brian200508/Marlin/docs/brsc/FTI-1.0.x/pictures/IMG_20200317_183908.jpg

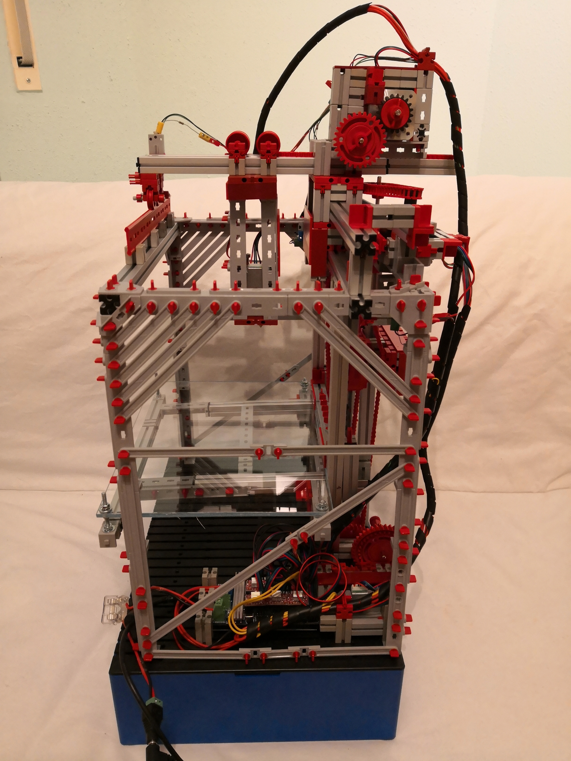
docs/brsc/FTI-1.0.x/pictures/IMG_20200317_183908.jpg
