brian200508/Marlin/docs/brsc/FTI-1.1.x/pictures/IMG_20200419_235620.jpg

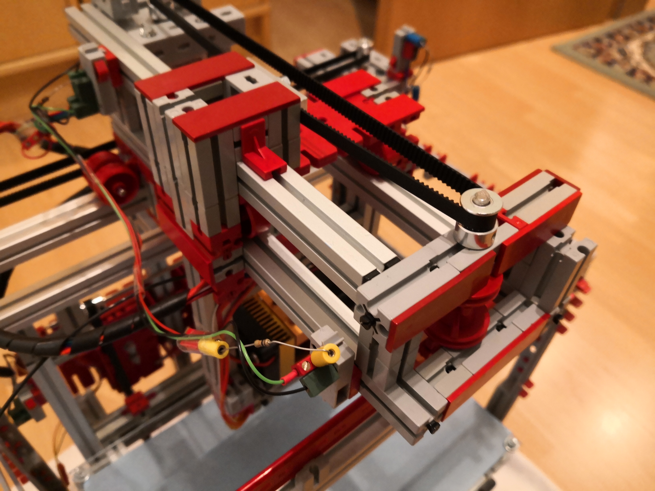
docs/brsc/FTI-1.1.x/pictures/IMG_20200419_235620.jpg
