brian200508/Marlin/docs/brsc/FTI-1.2.x/pictures/IMG_20200604_142323.jpg

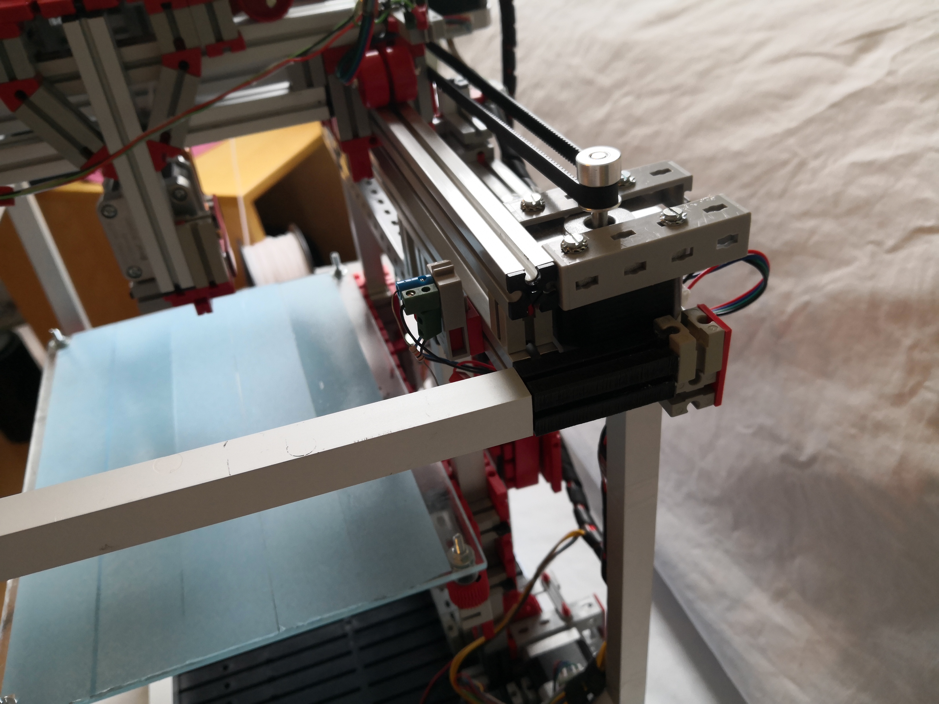
docs/brsc/FTI-1.2.x/pictures/IMG_20200604_142323.jpg
