brian200508/Marlin/docs/brsc/FTI-1.2.x/custom-parts/not-used/aluminum-square-tube-15x15-to-Fischertechnik-adapter-x-y-15-X-Z.png

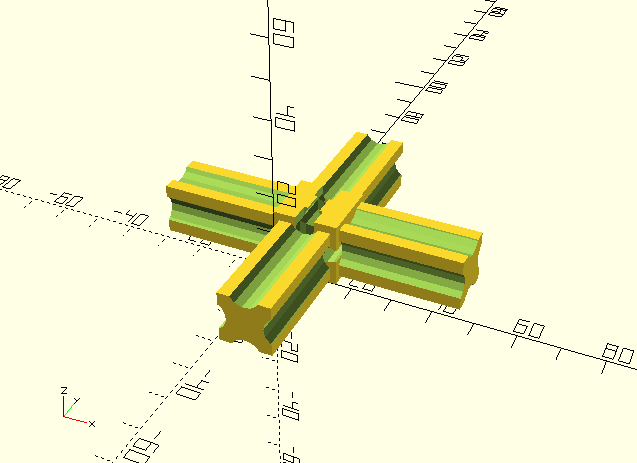
docs/brsc/FTI-1.2.x/custom-parts/not-used/aluminum-square-tube-15x15-to-Fischertechnik-adapter-x-y-15-X-Z.png
