brian200508/Marlin/docs/brsc/FTI-1.2.x/custom-parts/not-used/aluminum-square-tube-15x15-to-Fischertechnik-adapter-y-z-15-T.png

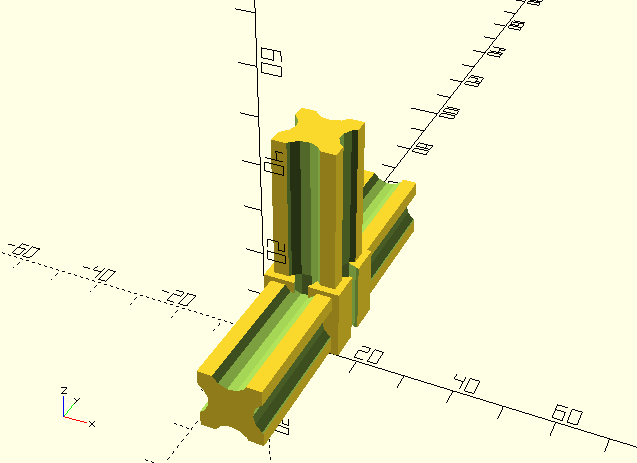
docs/brsc/FTI-1.2.x/custom-parts/not-used/aluminum-square-tube-15x15-to-Fischertechnik-adapter-y-z-15-T.png
