brian200508/Marlin/docs/brsc/FTI-1.2.x/custom-parts/not-used/axis-5mm-to-4mm-Fischertechnik-adapter.png

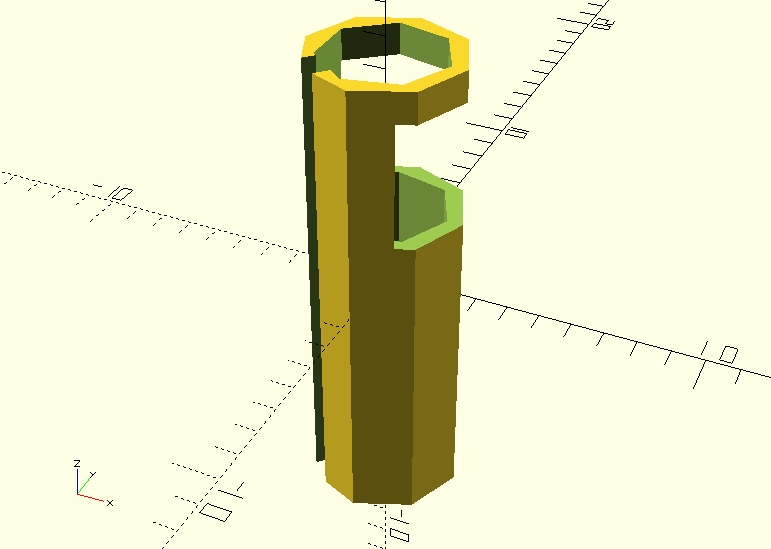
docs/brsc/FTI-1.2.x/custom-parts/not-used/axis-5mm-to-4mm-Fischertechnik-adapter.png
