brian200508/Marlin/docs/brsc/FTI-1.2.x/custom-parts/thingiverse/Belt_Tensioner_-_Reinforced/images/98af658794dd09332cecc4e60c305fb2_preview_featured.jpg

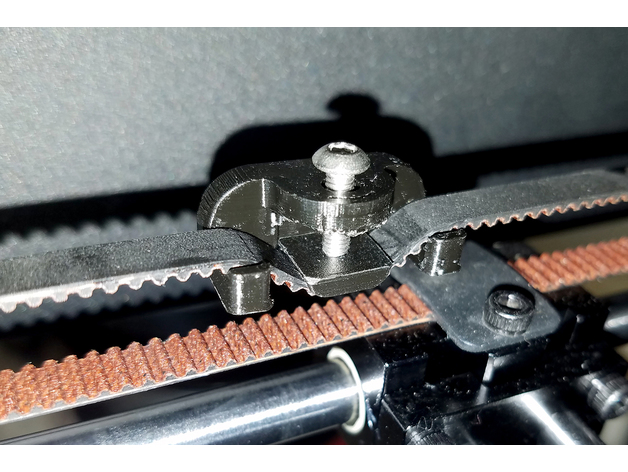
docs/brsc/FTI-1.2.x/custom-parts/thingiverse/Belt_Tensioner_-_Reinforced/images/98af658794dd09332cecc4e60c305fb2_preview_featured.jpg
