brian200508/Marlin/docs/brsc/FTI-1.2.x/custom-parts/thingiverse/Belt_Tensioner_-_Reinforced/images/16809a94bf5a926e6fb144e2bca0509e_preview_featured.jpg

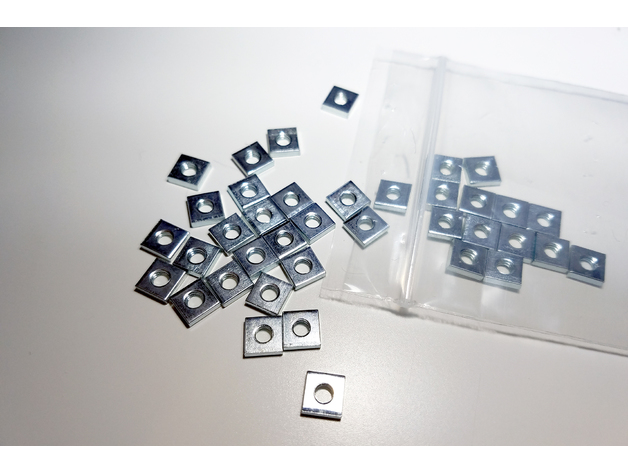
docs/brsc/FTI-1.2.x/custom-parts/thingiverse/Belt_Tensioner_-_Reinforced/images/16809a94bf5a926e6fb144e2bca0509e_preview_featured.jpg
