brian200508/Marlin/docs/brsc/FTI-1.2.x/custom-parts/thingiverse/Belt_Tensioner_-_Reinforced/images/d638693b8d8fdc0d19c9fbcd61633dfa_preview_featured.jpg

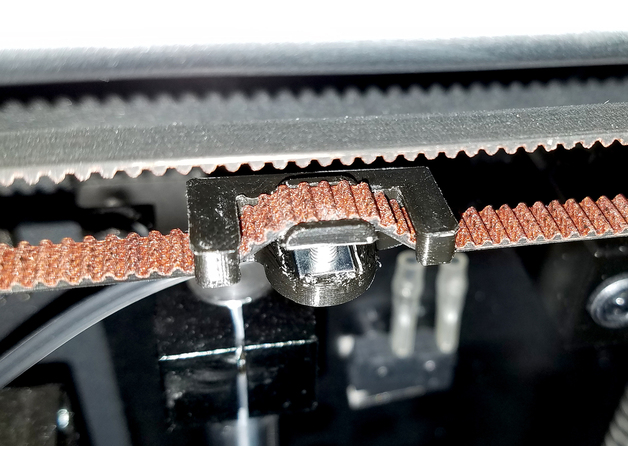
docs/brsc/FTI-1.2.x/custom-parts/thingiverse/Belt_Tensioner_-_Reinforced/images/d638693b8d8fdc0d19c9fbcd61633dfa_preview_featured.jpg
