brian200508/Marlin/docs/brsc/FTI-1.2.x/custom-parts/thingiverse/fischertechnik_double_flat_connector/images/2f4ae6def363fac59a60dda25eb9f56f_preview_featured.JPG

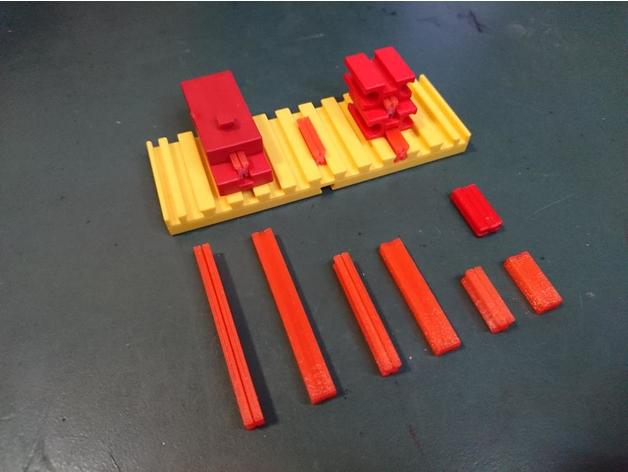
docs/brsc/FTI-1.2.x/custom-parts/thingiverse/fischertechnik_double_flat_connector/images/2f4ae6def363fac59a60dda25eb9f56f_preview_featured.JPG
