brian200508/Marlin/docs/brsc/FTI-1.2.x/custom-parts/thingiverse/fischertechnik_double_flat_connector/images/765520e2c20b9f5ceb8f800691d65215_preview_featured.jpg

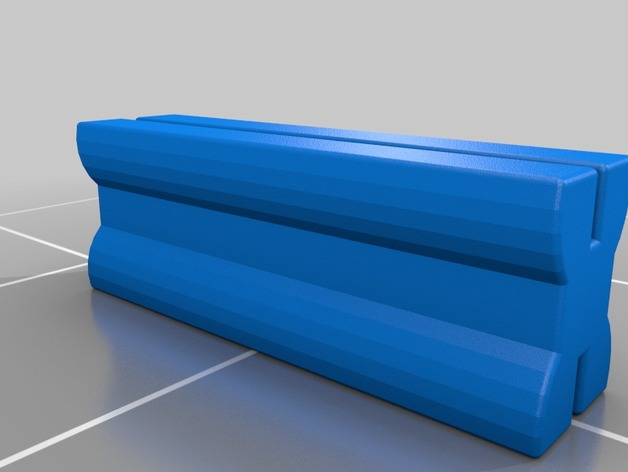
docs/brsc/FTI-1.2.x/custom-parts/thingiverse/fischertechnik_double_flat_connector/images/765520e2c20b9f5ceb8f800691d65215_preview_featured.jpg
