brian200508/Marlin/docs/brsc/FTI-1.2.x/custom-parts/thingiverse/fischertechnik_double_flat_connector/images/ac41eda1f4030cfab85e3fee53aedb6f_preview_featured.jpg

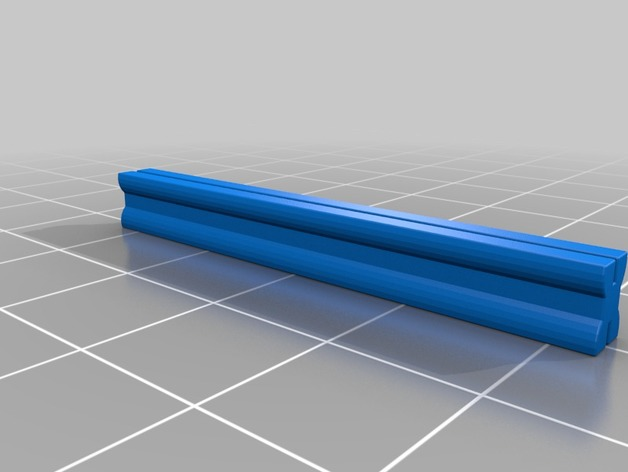
docs/brsc/FTI-1.2.x/custom-parts/thingiverse/fischertechnik_double_flat_connector/images/ac41eda1f4030cfab85e3fee53aedb6f_preview_featured.jpg
