brian200508/Marlin/docs/brsc/FTI-1.2.x/custom-parts/thingiverse/fischertechnik_double_flat_connector/images/b0776671d210ffe9cd5a600b5e34c5cb_preview_featured.jpg

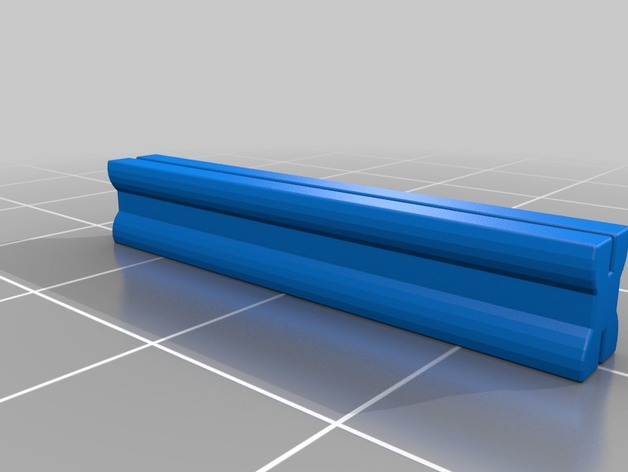
docs/brsc/FTI-1.2.x/custom-parts/thingiverse/fischertechnik_double_flat_connector/images/b0776671d210ffe9cd5a600b5e34c5cb_preview_featured.jpg
