brian200508/Marlin/docs/brsc/FTI-1.2.x/custom-parts/thingiverse/fischertechnik_double_flat_connector/images/d80029e1d572c3cbf382a6284b248c5f_preview_featured.jpg

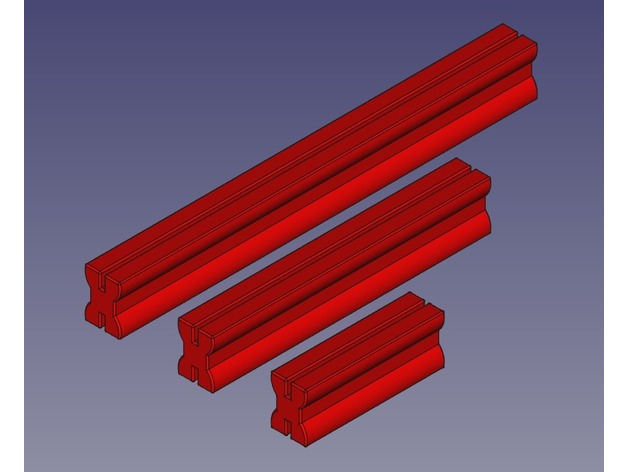
docs/brsc/FTI-1.2.x/custom-parts/thingiverse/fischertechnik_double_flat_connector/images/d80029e1d572c3cbf382a6284b248c5f_preview_featured.jpg
