brian200508/Marlin/docs/brsc/FTI-1.2.x/custom-parts/thingiverse/Fischertechnik_Double_GroovePin_SmartLab/images/058e439d927dcbf255e2c4b969152c6c_preview_featured.jpg

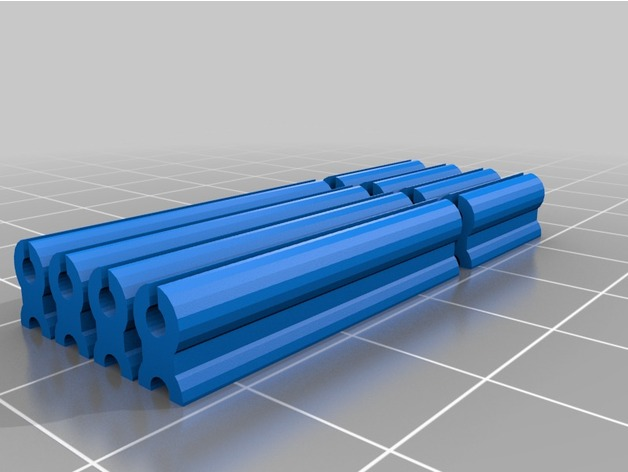
docs/brsc/FTI-1.2.x/custom-parts/thingiverse/Fischertechnik_Double_GroovePin_SmartLab/images/058e439d927dcbf255e2c4b969152c6c_preview_featured.jpg
