brian200508/Marlin/docs/brsc/FTI-1.2.x/custom-parts/thingiverse/Fischertechnik_Double_GroovePin_SmartLab/images/e607530fb95e5e1ce42673f375322e12_preview_featured.JPG

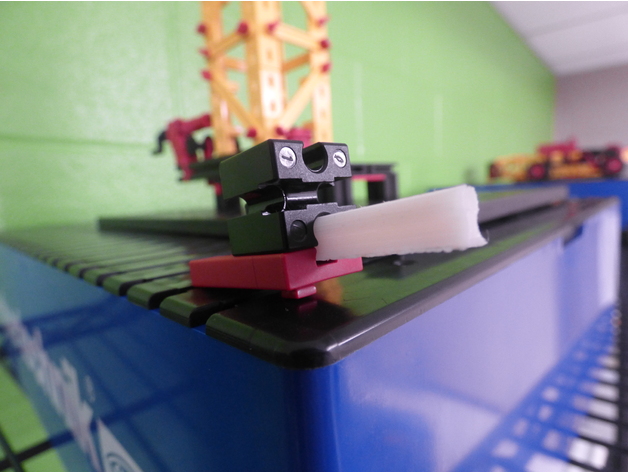
docs/brsc/FTI-1.2.x/custom-parts/thingiverse/Fischertechnik_Double_GroovePin_SmartLab/images/e607530fb95e5e1ce42673f375322e12_preview_featured.JPG
