brian200508/Marlin/docs/brsc/FTI-1.2.x/custom-parts/aluminum-square-tube-15x15-to-Fischertechnik-adapter-15.stl

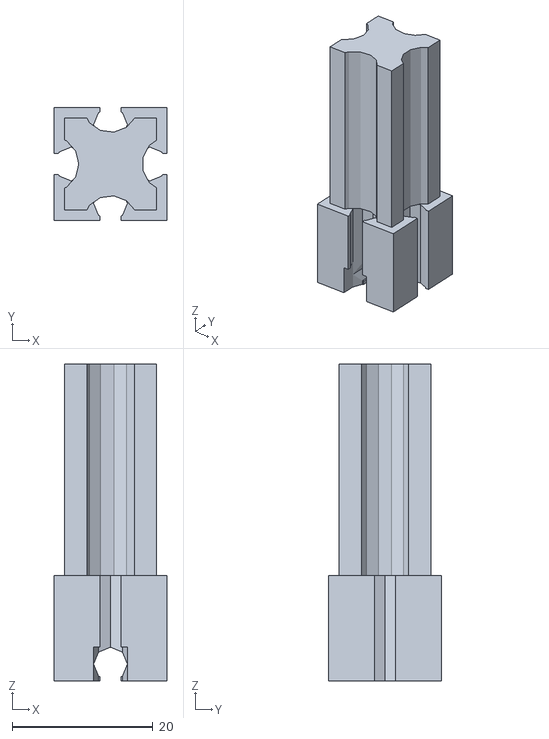
[picture p79: CAD file, 2020-05-04]
docs/brsc/FTI-1.2.x/custom-parts/aluminum-square-tube-15x15-to-Fischertechnik-adapter-15.stl
16.0 x 16.0 x 45.0
