brian200508/Marlin/docs/brsc/FTI-1.2.x/custom-parts/not-used/aluminum-square-tube-15x15-to-Fischertechnik-adapter-30.stl

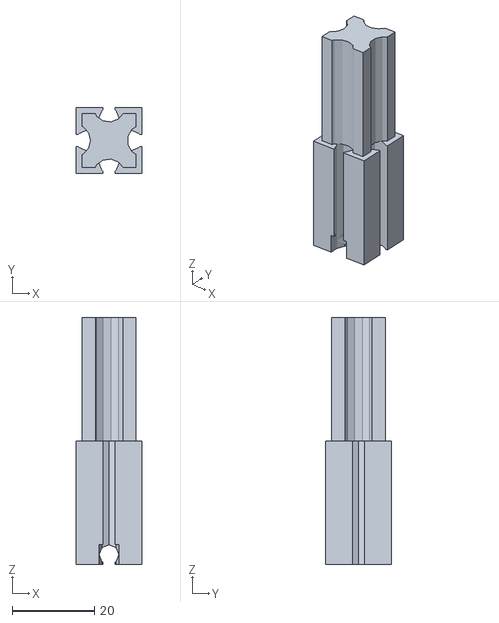
[picture p80: CAD file, 2020-05-04]
docs/brsc/FTI-1.2.x/custom-parts/not-used/aluminum-square-tube-15x15-to-Fischertechnik-adapter-30.stl
16.0 x 16.0 x 60.0
