brian200508/Marlin/docs/brsc/FTI-1.2.x/custom-parts/aluminum-square-tube-15x15-to-Fischertechnik-adapter-x-y-z-15-R.stl

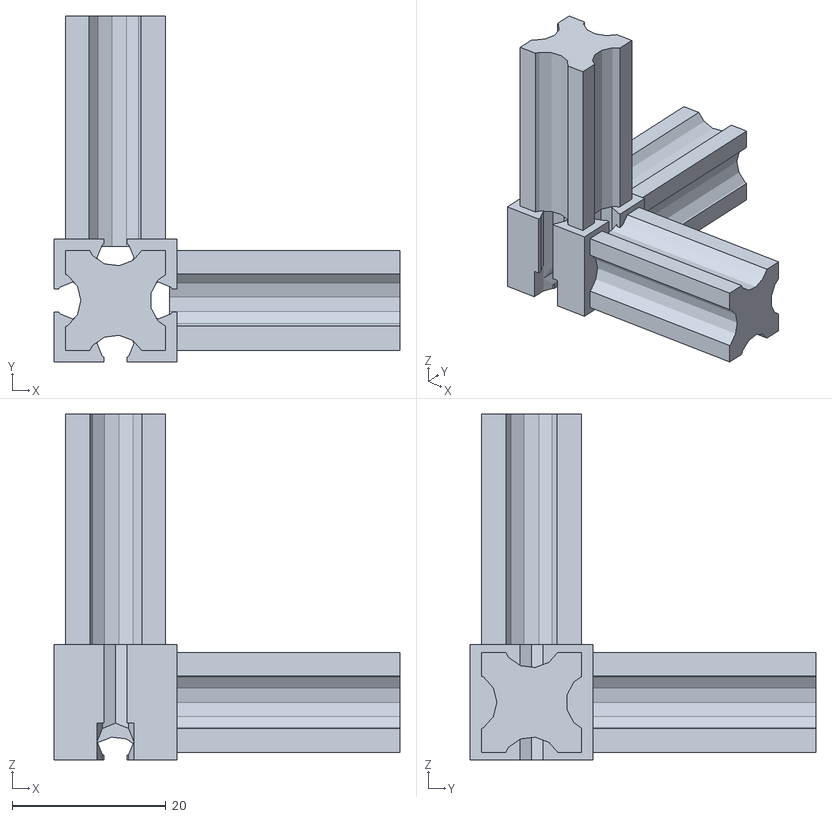
[picture p81: CAD file, 2020-05-04]
docs/brsc/FTI-1.2.x/custom-parts/aluminum-square-tube-15x15-to-Fischertechnik-adapter-x-y-z-15-R.stl
45.0 x 45.0 x 45.0
