brian200508/Marlin/docs/brsc/FTI-1.2.x/custom-parts/not-used/Fischertechnik-compatible-building-block-with-hole-90.stl

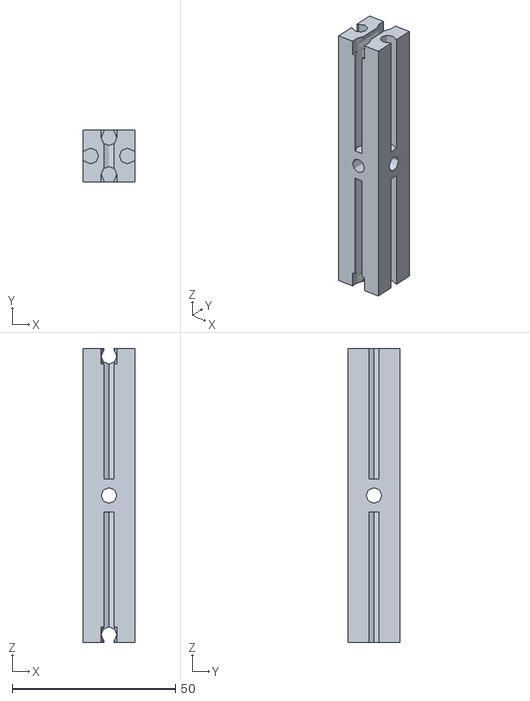
[picture p82: CAD file, 2020-04-23]
docs/brsc/FTI-1.2.x/custom-parts/not-used/Fischertechnik-compatible-building-block-with-hole-90.stl
16.0 x 16.0 x 90.0
