brian200508/Marlin/docs/brsc/FTI-1.2.x/pictures/intermediate-step-1/IMG_20200503_225055.jpg

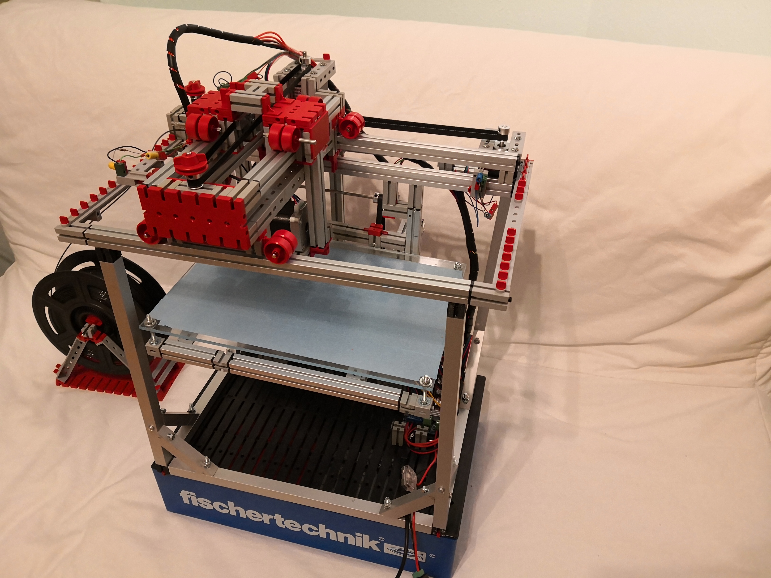
docs/brsc/FTI-1.2.x/pictures/intermediate-step-1/IMG_20200503_225055.jpg
