brian200508/Marlin/docs/brsc/FTI-1.2.x/pictures/intermediate-step-1/IMG_20200503_230231.jpg

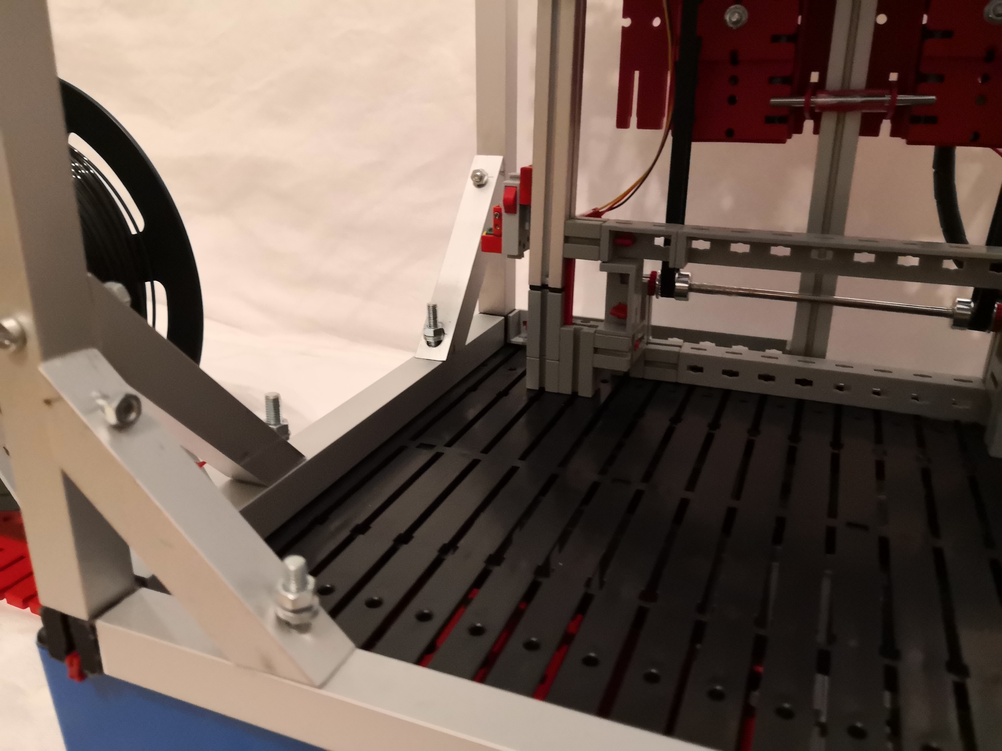
docs/brsc/FTI-1.2.x/pictures/intermediate-step-1/IMG_20200503_230231.jpg
