brian200508/Marlin/docs/brsc/FTI-1.2.x/pictures/intermediate-step-2/IMG_20200513_233617.jpg

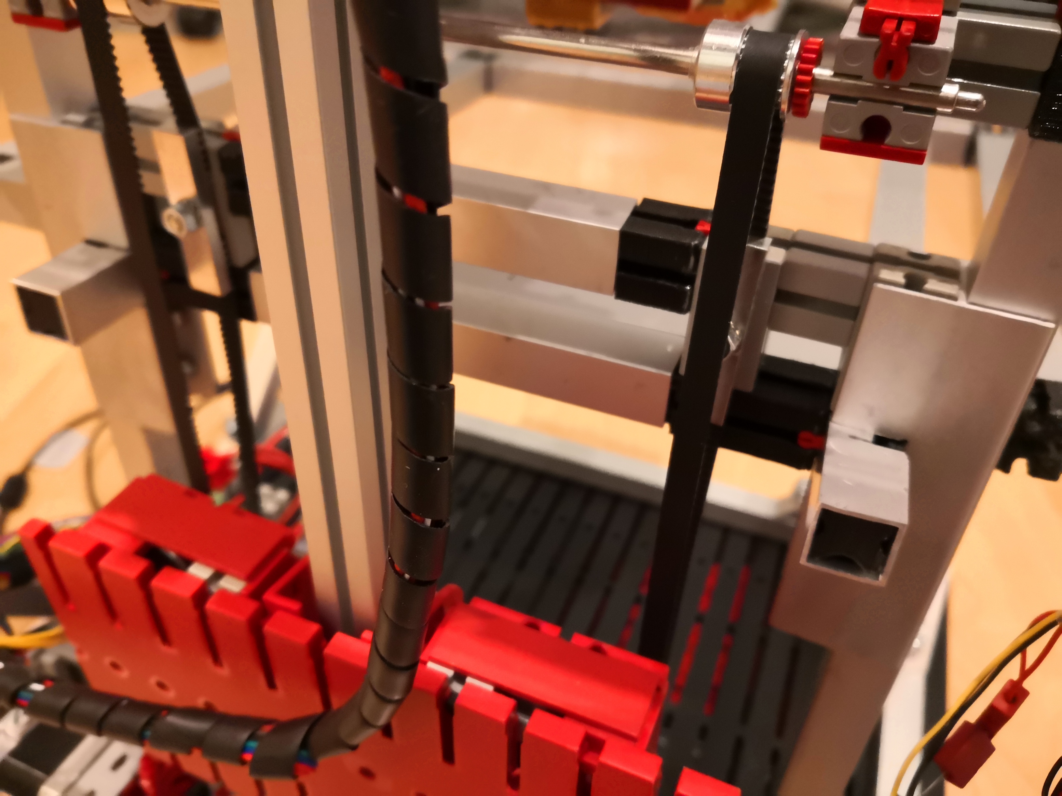
docs/brsc/FTI-1.2.x/pictures/intermediate-step-2/IMG_20200513_233617.jpg
