brian200508/Marlin/docs/brsc/FTI-1.2.x/pictures/intermediate-step-3/IMG_20200514_130701.jpg

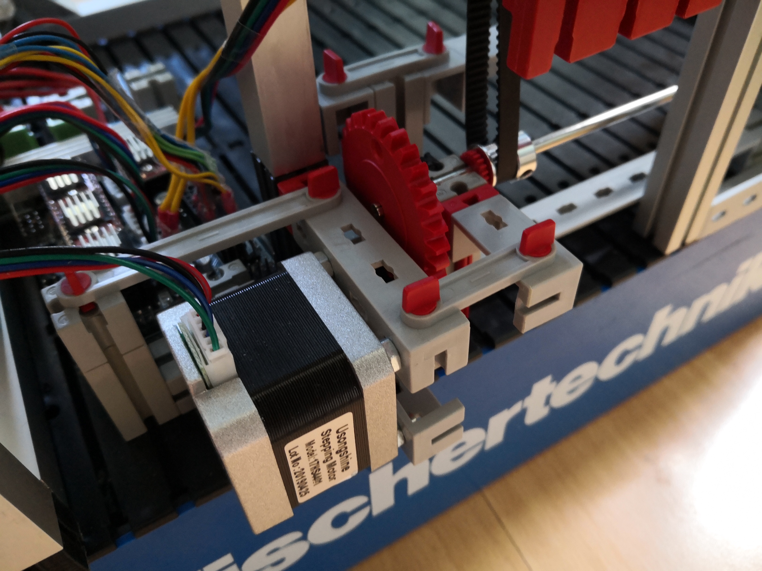
docs/brsc/FTI-1.2.x/pictures/intermediate-step-3/IMG_20200514_130701.jpg
