brian200508/Marlin/docs/brsc/FTI-1.2.x/pictures/intermediate-step-3/IMG_20200514_151922.jpg

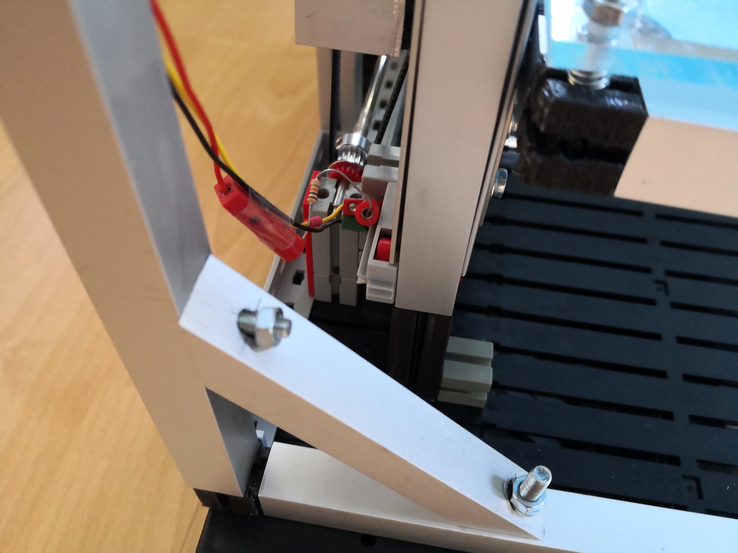
docs/brsc/FTI-1.2.x/pictures/intermediate-step-3/IMG_20200514_151922.jpg
