brian200508/Marlin/docs/brsc/FTI-1.2.x/pictures/intermediate-step-4/IMG_20200514_152306.jpg

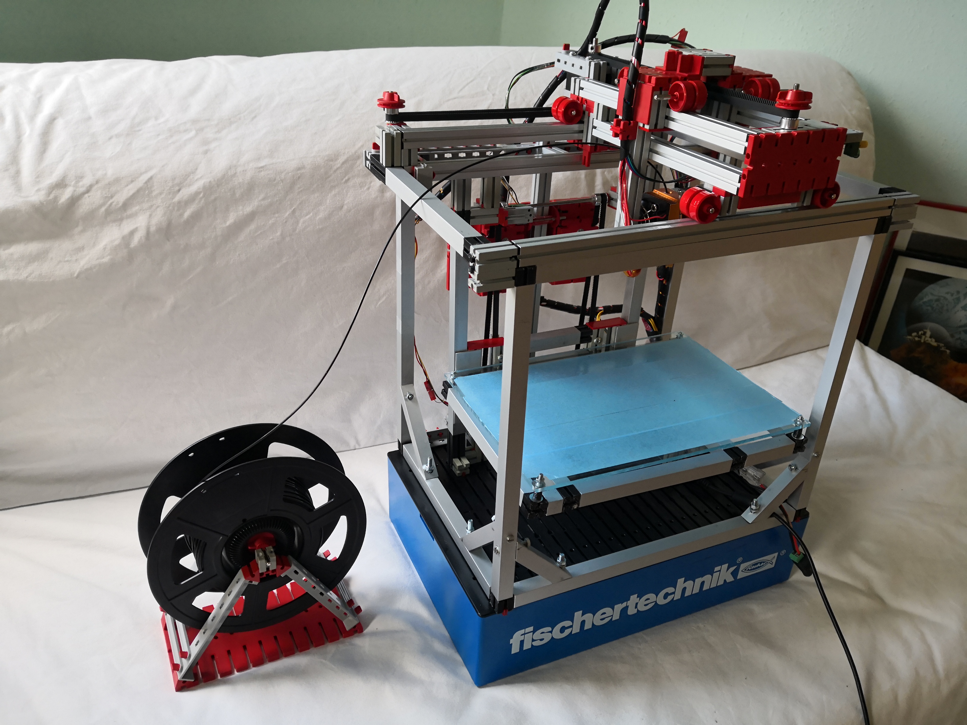
docs/brsc/FTI-1.2.x/pictures/intermediate-step-4/IMG_20200514_152306.jpg
