brian200508/Marlin/docs/brsc/FTI-1.2.x/pictures/intermediate-step-4/IMG_20200514_152324.jpg

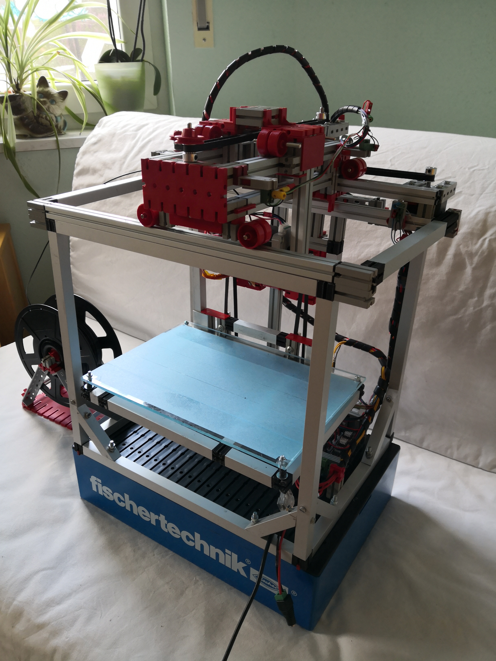
docs/brsc/FTI-1.2.x/pictures/intermediate-step-4/IMG_20200514_152324.jpg
