brian200508/Marlin/docs/brsc/FTI-1.2.x/pictures/intermediate-step-5/IMG_20200514_191553.jpg

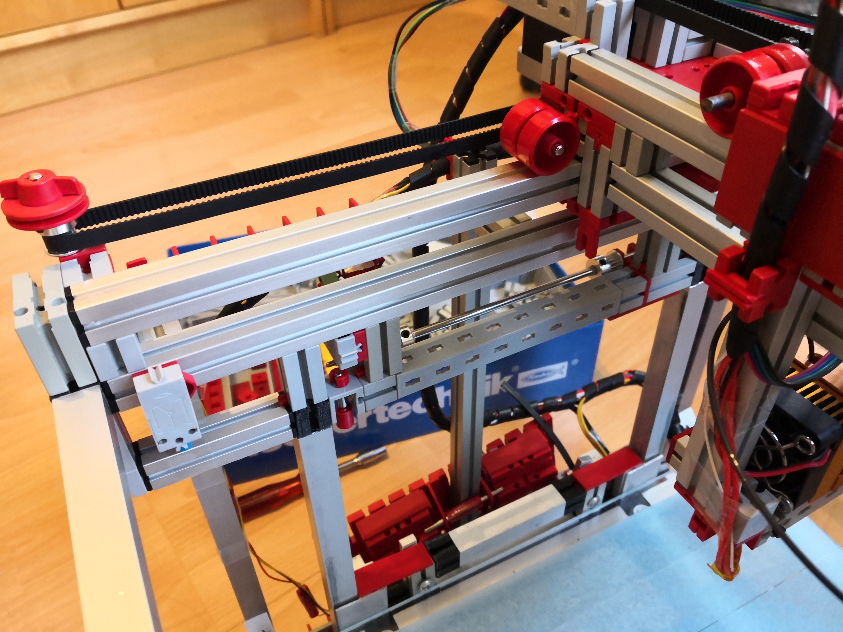
docs/brsc/FTI-1.2.x/pictures/intermediate-step-5/IMG_20200514_191553.jpg
