brian200508/Marlin/docs/brsc/FTI-1.2.x/pictures/intermediate-step-5/IMG_20200519_131153.jpg

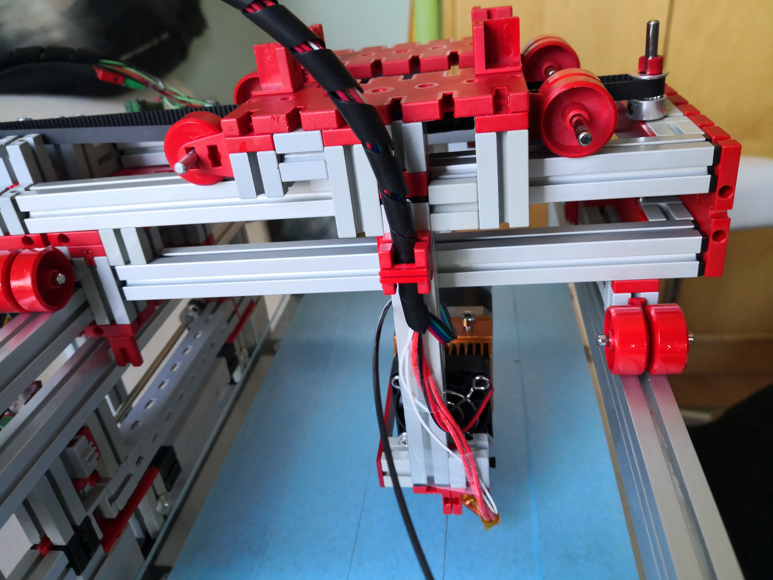
docs/brsc/FTI-1.2.x/pictures/intermediate-step-5/IMG_20200519_131153.jpg
