brian200508/Marlin/docs/brsc/FTI-1.2.x/pictures/intermediate-step-6-FTI-1.2.1/IMG_20200514_114907.jpg

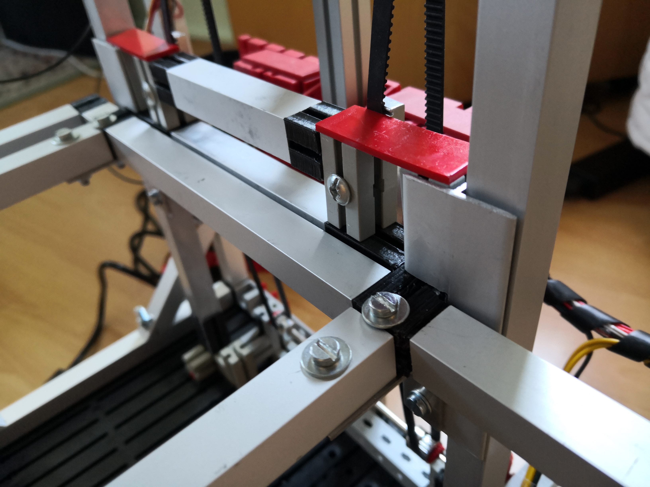
docs/brsc/FTI-1.2.x/pictures/intermediate-step-6-FTI-1.2.1/IMG_20200514_114907.jpg
