brian200508/Marlin/docs/brsc/FTI-1.2.x/pictures/intermediate-step-7/IMG_20200604_102751.jpg

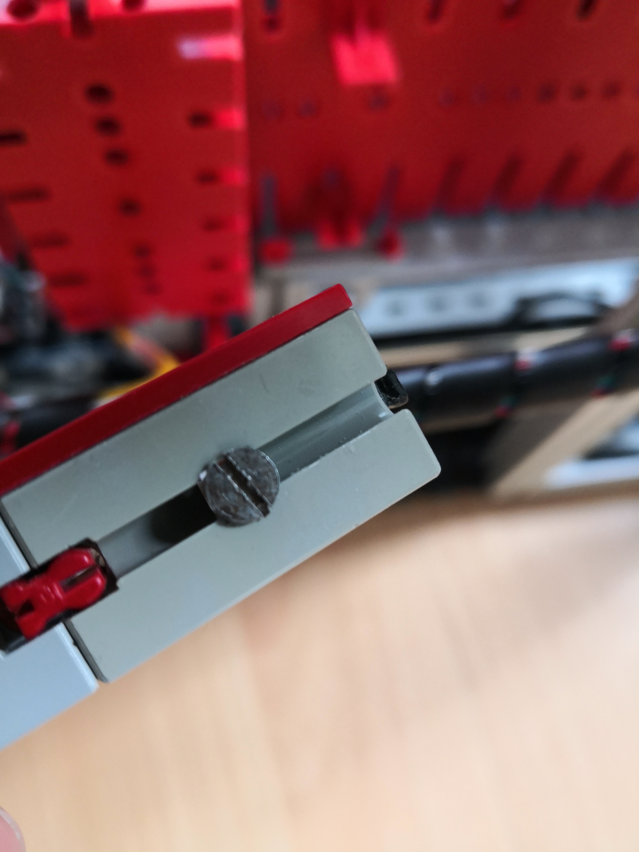
docs/brsc/FTI-1.2.x/pictures/intermediate-step-7/IMG_20200604_102751.jpg
